rcaproni/bttf_clock/code/bttf_clock/src/mySlowSoftI2CMaster.cpp

/* Arduino Slow Software I2C Master 
   Copyright (c) 2017 Bernhard Nebel.

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
   You should have received a copy of the GNU Lesser General Public
   License along with this library; if not, write to the Free Software
   Foundation, Inc., 51 Franklin St, Fifth Floor, Boston, MA 02110-1301
   USA
*/

// Modified by Rodolfo Caproni
// 

#include <mySlowSoftI2CMaster.h>

mySlowSoftI2CMaster::mySlowSoftI2CMaster(uint8_t sda, uint8_t scl) {
  _sda = sda;
  _scl = scl;
  _pullup = false;
}

mySlowSoftI2CMaster::mySlowSoftI2CMaster(uint8_t sda, uint8_t scl, bool pullup) {
  _sda = sda;
  _scl = scl;
  _pullup = pullup;
}
// Init function. Needs to be called once in the beginning.
// Returns false if SDA or SCL are low, which probably means 
// a I2C bus lockup or that the lines are not pulled up.
bool mySlowSoftI2CMaster::i2c_init(void) {
  digitalWrite(_sda, LOW);
  digitalWrite(_scl, LOW);
  setHigh(_sda);
  setHigh(_scl);
  if (digitalRead(_sda) == LOW )
    Serial.println("erro sda"); 
  if(digitalRead(_scl) == LOW)
    Serial.println("erro scl"); 

  if (digitalRead(_sda) == LOW || digitalRead(_scl) == LOW) return false;
  return true;
}

// Start transfer function: <addr> is the 8-bit I2C address (including the R/W
// bit). 
// Return: true if the slave replies with an "acknowledge", false otherwise
bool mySlowSoftI2CMaster::i2c_start(uint8_t addr) {
  setLow(_sda);
  delayMicroseconds(DELAY);
  setLow(_scl);
  return i2c_write(addr);
}

// Added by Rodolfo
// Init I2c without sending a write. Only I2C START command is sent.
void mySlowSoftI2CMaster::i2c_start_disp() {
  setLow(_sda);
  delayMicroseconds(DELAY);
  setLow(_scl);

}

// Try to start transfer until an ACK is returned
bool mySlowSoftI2CMaster::i2c_start_wait(uint8_t addr) {
  long retry = I2C_MAXWAIT;
  while (!i2c_start(addr)) {
    i2c_stop();
    if (--retry == 0) return false;
  }
  return true;
}

// Repeated start function: After having claimed the bus with a start condition,
// you can address another or the same chip again without an intervening 
// stop condition.
// Return: true if the slave replies with an "acknowledge", false otherwise
bool mySlowSoftI2CMaster::i2c_rep_start(uint8_t addr) {
  setHigh(_sda);
  setHigh(_scl);
  delayMicroseconds(DELAY);
  return i2c_start(addr);
}

// Issue a stop condition, freeing the bus.
void mySlowSoftI2CMaster::i2c_stop(void) {
  setLow(_sda);
  delayMicroseconds(DELAY);
  setHigh(_scl);
  delayMicroseconds(DELAY);
  setHigh(_sda);
  delayMicroseconds(DELAY);
}

// Write one byte to the slave chip that had been addressed
// by the previous start call. <value> is the byte to be sent.
// Return: true if the slave replies with an "acknowledge", false otherwise
bool mySlowSoftI2CMaster::i2c_write(uint8_t value) {
  for (uint8_t curr = 0X80; curr != 0; curr >>= 1) {
    if (curr & value) 
      setHigh(_sda); 
    else  setLow(_sda); 
    setHigh(_scl);
    delayMicroseconds(DELAY);
    setLow(_scl);
  }
  // get Ack or Nak
  setHigh(_sda);
  setHigh(_scl);
  delayMicroseconds(DELAY/2);
  uint8_t ack = digitalRead(_sda);
  setLow(_scl);
  delayMicroseconds(DELAY/2);  
  setLow(_sda);
  return ack == 0;
}

bool mySlowSoftI2CMaster::i2c_write_lsb(uint8_t value) {
  for (uint8_t curr = 0X1; curr != 0; curr <<= 1) {
    if (curr & value) 
      setHigh(_sda); 
    else  setLow(_sda); 
    setHigh(_scl);
    delayMicroseconds(DELAY);
    setLow(_scl);
  }
  // get Ack or Nak
  setHigh(_sda);
  setHigh(_scl);
  delayMicroseconds(DELAY/2);
  uint8_t ack = digitalRead(_sda);
  setLow(_scl);
  delayMicroseconds(DELAY/2);  
  setLow(_sda);
  return ack == 0;
}

// Read one byte. If <last> is true, we send a NAK after having received 
// the byte in order to terminate the read sequence. 
uint8_t mySlowSoftI2CMaster::i2c_read(bool last) {
  uint8_t b = 0;
  setHigh(_sda);
  for (uint8_t i = 0; i < 8; i++) {
    b <<= 1;
    delayMicroseconds(DELAY);
    setHigh(_scl);
    if (digitalRead(_sda)) b |= 1;
    setLow(_scl);
  }
  if (last) setHigh(_sda); else setLow(_sda);
  setHigh(_scl);
  delayMicroseconds(DELAY/2);
  setLow(_scl);
  delayMicroseconds(DELAY/2);  
  setLow(_sda);
  return b;
}

void mySlowSoftI2CMaster::setLow(uint8_t pin) {
    noInterrupts();
    if (_pullup) 
      digitalWrite(pin, LOW);
    pinMode(pin, OUTPUT);
    interrupts();
}



// modified by Rodolfo Caproni
// Change the pin mode and wrtie HIGH to amke it work with the RTC
void mySlowSoftI2CMaster::setHigh(uint8_t pin) {
    noInterrupts();
    pinMode(pin, OUTPUT);
    digitalWrite(pin, HIGH);
    if (_pullup) 
      pinMode(pin, INPUT_PULLUP);
    else
      pinMode(pin, INPUT);
    interrupts();
}
